asugden/bebox/3d/wheel/wheel.stl

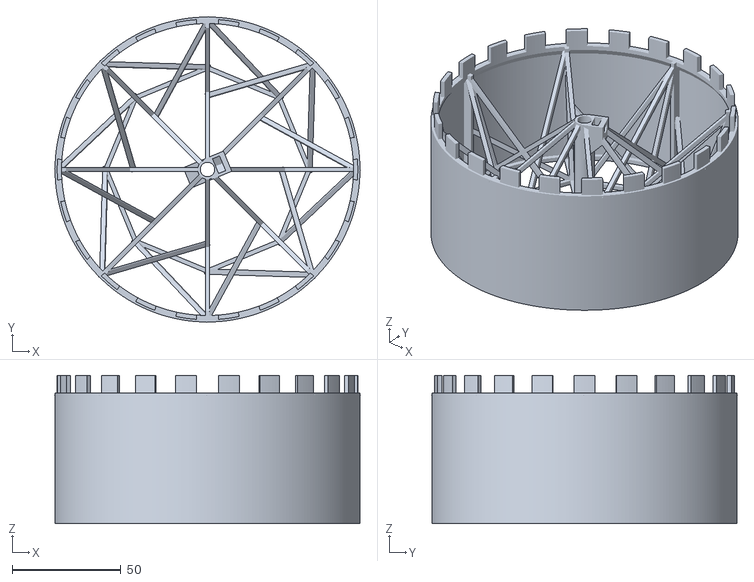
[picture p15: CAD file, 2019-01-22]
3d/wheel/wheel.stl
140.5 x 140.5 x 68.0
