asugden/bebox/3d/lickspout/lickspout bitube.stl

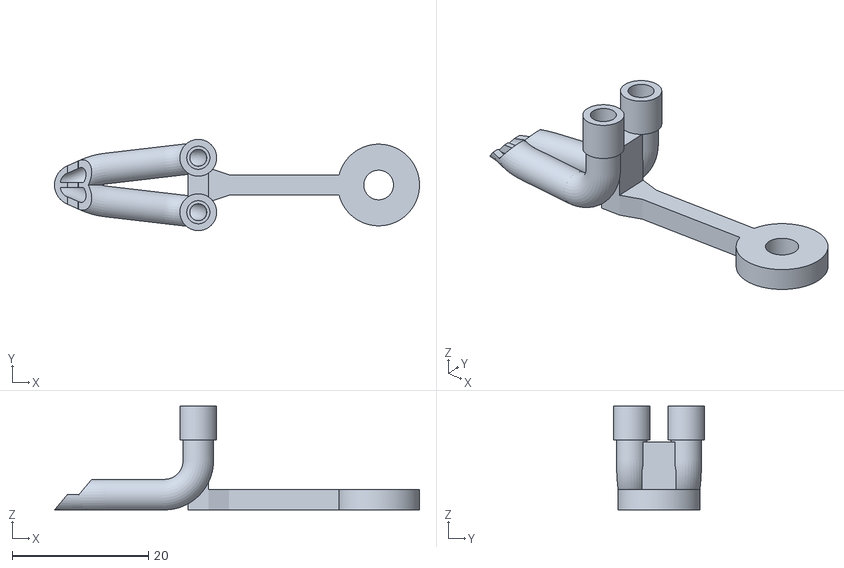
[picture p16: CAD file, 2019-01-28]
3d/lickspout/lickspout bitube.stl
53.6 x 13.4 x 15.2
