asugden/bebox/3d/bebox/bebox button bottom.stl

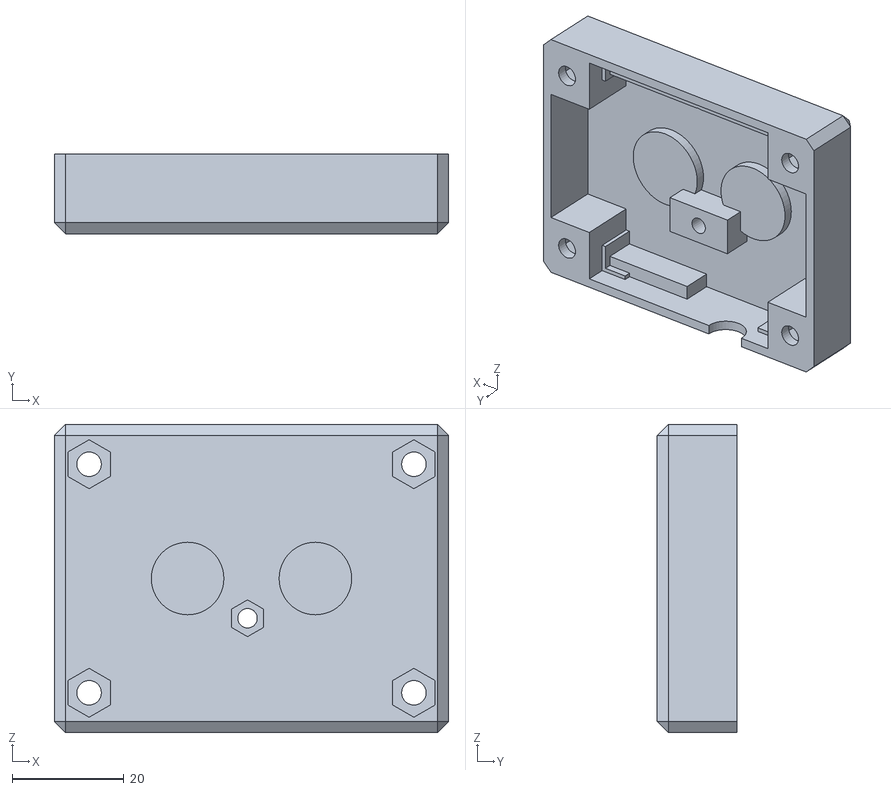
[picture p17: CAD file, 2019-04-11]
3d/bebox/bebox button bottom.stl
70.6 x 14.3 x 55.2
