asugden/bebox/3d/bebox/bebox bnc bottom.stl

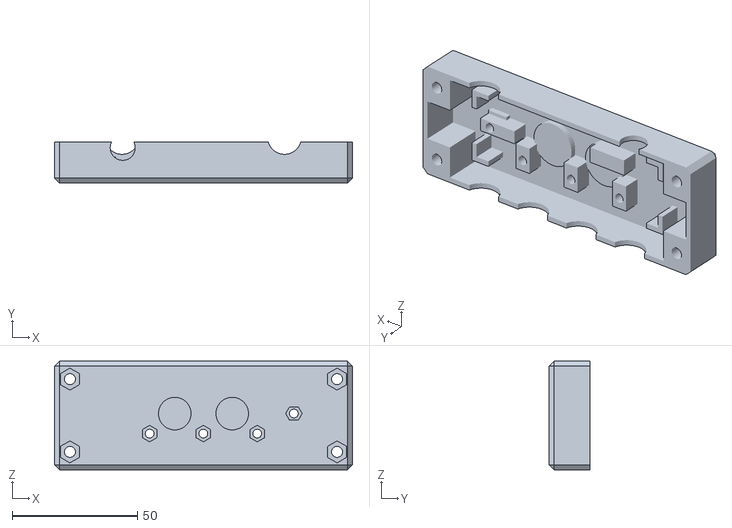
[picture p18: CAD file, 2019-04-11]
3d/bebox/bebox bnc bottom.stl
118.8 x 16.5 x 43.3
