asugden/bebox/3d/bebox/bebox button 1.stl

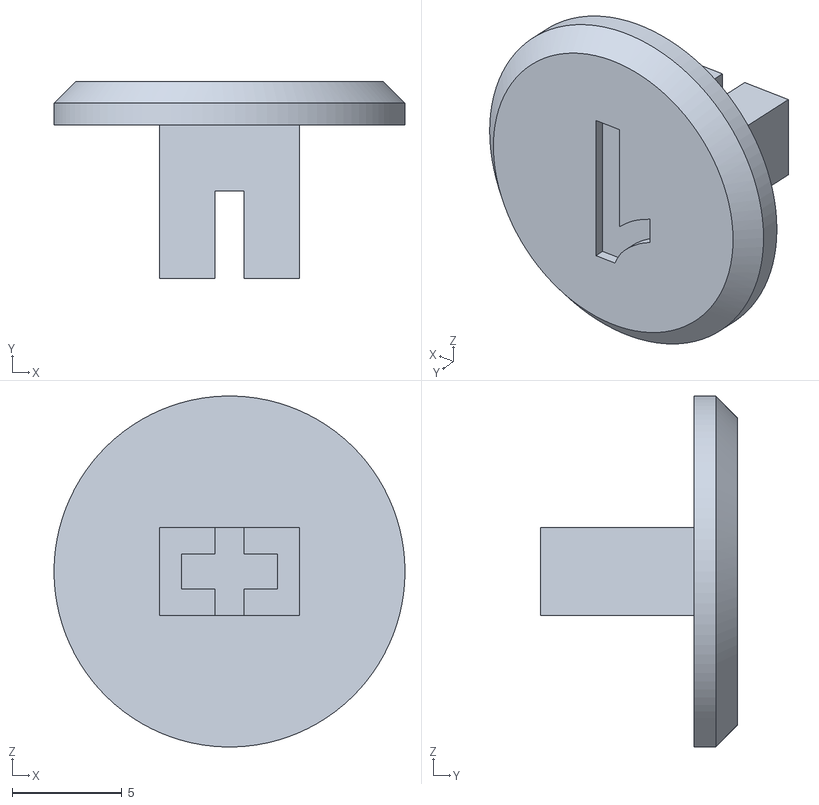
[picture p19: CAD file, 2019-04-11]
3d/bebox/bebox button 1.stl
16.0 x 9.00 x 16.0
