asugden/bebox/3d/bebox/bebox button top.stl

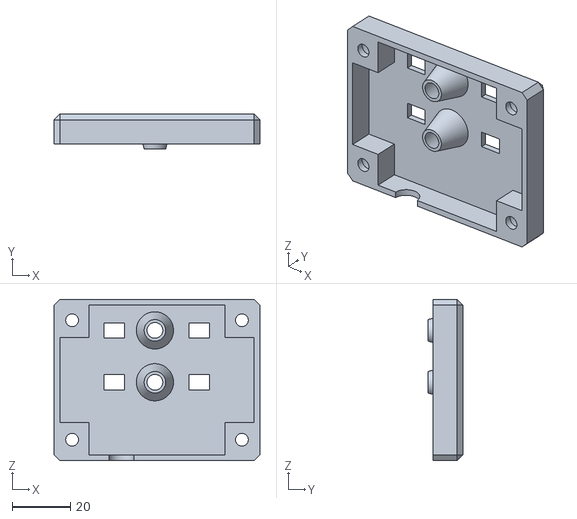
[picture p20: CAD file, 2019-04-11]
3d/bebox/bebox button top.stl
70.6 x 12.0 x 55.2
