asugden/bebox/arduino/Spritz/Montserrat_Medium20pt7b.h

const uint8_t Montserrat_Medium20pt7bBitmaps[] PROGMEM = {
  0xF7, 0xBD, 0xEF, 0x7B, 0xDE, 0xF7, 0xBD, 0xE7, 0x39, 0xCE, 0x73, 0x9C,
  0x00, 0x01, 0xDF, 0xFF, 0xDC, 0xF0, 0xFE, 0x1D, 0xC3, 0xB8, 0x77, 0x0E,
  0xE1, 0xDC, 0x3B, 0x87, 0x70, 0xEE, 0x1D, 0xC3, 0x80, 0x00, 0xE0, 0x38,
  0x00, 0x70, 0x1C, 0x00, 0x30, 0x0E, 0x00, 0x38, 0x06, 0x00, 0x1C, 0x03,
  0x00, 0x0E, 0x03, 0x81, 0xFF, 0xFF, 0xFE, 0xFF, 0xFF, 0xFF, 0x7F, 0xFF,
  0xFF, 0x80, 0xE0, 0x38, 0x00, 0x60, 0x1C, 0x00, 0x70, 0x0C, 0x00, 0x38,
  0x06, 0x00, 0x1C, 0x07, 0x00, 0x0E, 0x03, 0x80, 0x07, 0x01, 0xC0, 0x03,
  0x80, 0xE0, 0x7F, 0xFF, 0xFF, 0xBF, 0xFF, 0xFF, 0xDF, 0xFF, 0xFF, 0xE0,
  0x70, 0x0C, 0x00, 0x38, 0x0E, 0x00, 0x1C, 0x07, 0x00, 0x0E, 0x03, 0x80,
  0x07, 0x01, 0xC0, 0x03, 0x80, 0xE0, 0x01, 0x80, 0x70, 0x00, 0x00, 0x70,
  0x00, 0x03, 0x80, 0x00, 0x1C, 0x00, 0x00, 0xE0, 0x00, 0x07, 0x00, 0x00,
  0x38, 0x00, 0x0F, 0xF8, 0x01, 0xFF, 0xF8, 0x3F, 0xFF, 0xF1, 0xFB, 0x9F,
  0x1F, 0x1C, 0x18, 0xF0, 0xE0, 0x4F, 0x07, 0x00, 0x78, 0x38, 0x03, 0xC1,
  0xC0, 0x0F, 0x0E, 0x00, 0x7C, 0x70, 0x01, 0xFF, 0x80, 0x07, 0xFE, 0x00,
  0x1F, 0xFE, 0x00, 0x1F, 0xFC, 0x00, 0x3F, 0xF0, 0x01, 0xCF, 0xC0, 0x0E,
  0x1E, 0x00, 0x70, 0x78, 0x03, 0x83, 0xC0, 0x1C, 0x1E, 0x80, 0xE1, 0xEF,
  0x07, 0x0F, 0x7F, 0x3B, 0xF9, 0xFF, 0xFF, 0x87, 0xFF, 0xF0, 0x07, 0xFE,
  0x00, 0x03, 0x80, 0x00, 0x1C, 0x00, 0x00, 0xE0, 0x00, 0x07, 0x00, 0x00,
  0x0F, 0x80, 0x01, 0xC0, 0x3F, 0xC0, 0x07, 0x00, 0xE3, 0xC0, 0x0E, 0x03,
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
  {  2111,  19,  27,  25,    4,  -26 },   // 0x46 'F'
  {  2176,  25,  27,  30,    2,  -26 },   // 0x47 'G'
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

const GFXfont Montserrat_Medium20pt7b PROGMEM = {
  (uint8_t  *)Montserrat_Medium20pt7bBitmaps,
  (GFXglyph *)Montserrat_Medium20pt7bGlyphs,
  0x20, 0x7E, 48 };

// Approx. 6341 bytes
