asugden/bebox/arduino/Spritz/Montserrat_Regular6pt7b.h

const uint8_t Montserrat_Regular6pt7bBitmaps[] PROGMEM = {
  0xFC, 0x80, 0xB6, 0x80, 0x12, 0x24, 0x7F, 0x24, 0x24, 0x24, 0xFE, 0x24,
  0x24, 0x20, 0x87, 0xA9, 0xA2, 0x87, 0x0A, 0x26, 0x9F, 0x88, 0xE2, 0xA4,
  0xA4, 0xA8, 0xD6, 0x15, 0x29, 0x49, 0x47, 0x70, 0x91, 0x22, 0x86, 0x12,
  0xA3, 0x46, 0x72, 0x54, 0x56, 0xAA, 0xA5, 0x40, 0xC9, 0x22, 0x49, 0x29,
  0x2C, 0x2F, 0x2F, 0x20, 0x21, 0x09, 0xF2, 0x10, 0xE0, 0xE0, 0x80, 0x11,
  0x11, 0x22, 0x24, 0x44, 0x88, 0x80, 0x7A, 0x28, 0x61, 0x86, 0x18, 0x62,
  0x78, 0xE4, 0x92, 0x49, 0x20, 0x7A, 0x10, 0x41, 0x08, 0x42, 0x10, 0xFC,
  0xFC, 0x21, 0x04, 0x38, 0x10, 0x61, 0x78, 0x0C, 0x08, 0x10, 0x20, 0x24,
  0x44, 0xFF, 0x04, 0x04, 0x7D, 0x04, 0x1E, 0x04, 0x10, 0x61, 0x78, 0x7A,
  0x08, 0x3E, 0x8A, 0x18, 0x62, 0x78, 0xFE, 0x10, 0x42, 0x08, 0x41, 0x04,
  0x20, 0x7A, 0x28, 0x62, 0x7A, 0x18, 0x61, 0x78, 0x78, 0x8A, 0x12, 0x37,
  0xA0, 0x41, 0x02, 0x78, 0x84, 0x87, 0x09, 0xB1, 0xC1, 0x80, 0xF8, 0x01,
  0xF0, 0x83, 0x06, 0x6C, 0x00, 0x7A, 0x10, 0x41, 0x08, 0x41, 0x00, 0x10,
  0x1F, 0x0C, 0x12, 0x7D, 0x50, 0xAA, 0x13, 0x42, 0x68, 0x4D, 0x0A, 0x9E,
  0xD0, 0x01, 0x80, 0x0F, 0x80, 0x08, 0x18, 0x14, 0x24, 0x22, 0x42, 0x7E,
  0x41, 0x81, 0xFD, 0x06, 0x0C, 0x1F, 0xD0, 0x60, 0xC1, 0xFC, 0x3C, 0x86,
  0x04, 0x08, 0x10, 0x20, 0x21, 0x3C, 0xFC, 0x82, 0x81, 0x81, 0x81, 0x81,
  0x81, 0x82, 0xFC, 0xFE, 0x08, 0x20, 0xFA, 0x08, 0x20, 0xFC, 0xFE, 0x08,
  0x20, 0xFA, 0x08, 0x20, 0x80, 0x3C, 0x86, 0x04, 0x08, 0x30, 0x60, 0xA1,
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
  {   214,   6,   9,   7,    1,   -8 },   // 0x46 'F'
  {   221,   7,   9,   9,    1,   -8 },   // 0x47 'G'
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

const GFXfont Montserrat_Regular6pt7b PROGMEM = {
  (uint8_t  *)Montserrat_Regular6pt7bBitmaps,
  (GFXglyph *)Montserrat_Regular6pt7bGlyphs,
  0x20, 0x7E, 14 };

// Approx. 1258 bytes
